telzo2000/cool642tb/img/img00017.jpg

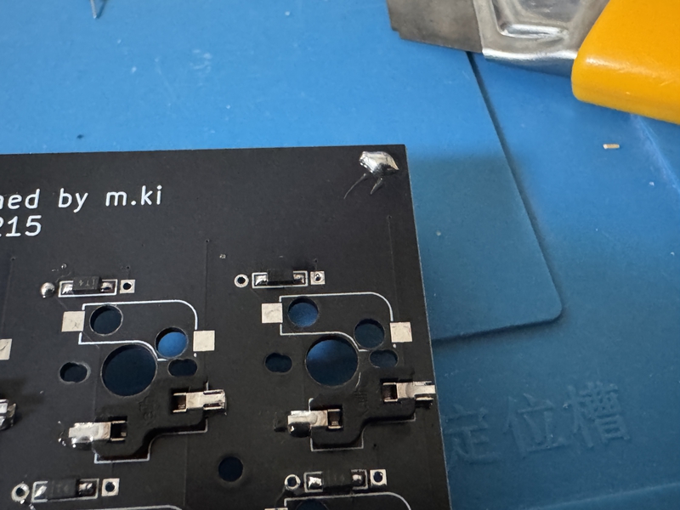
img/img00017.jpg
