telzo2000/cool642tb/img/img00023.jpg

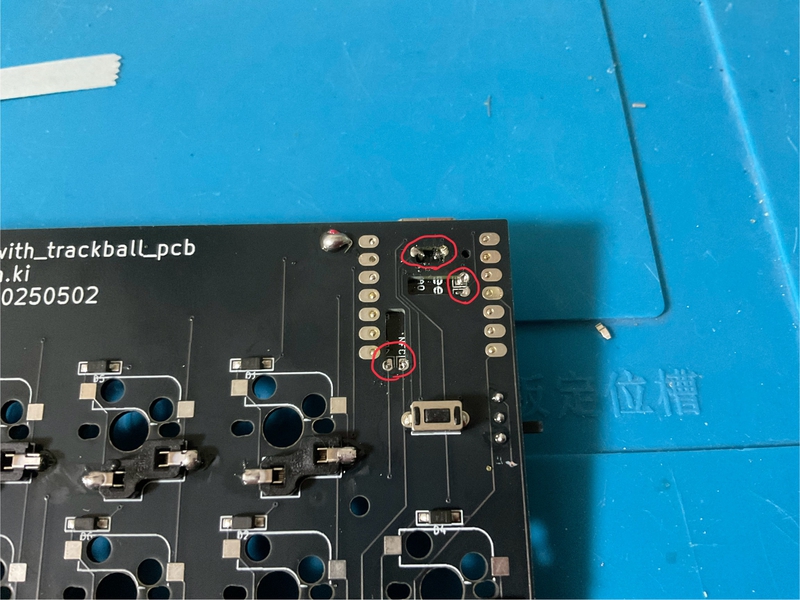
img/img00023.jpg
