telzo2000/cool642tb/img/img00024.jpg

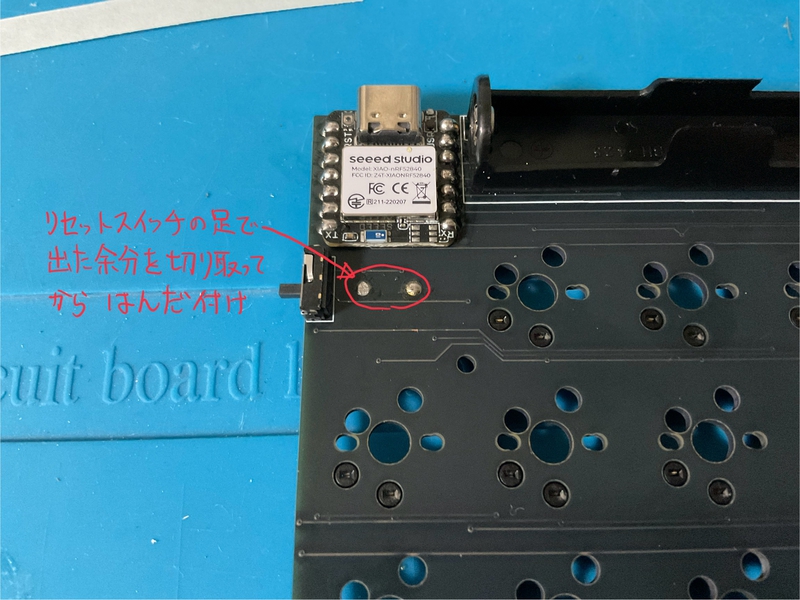
img/img00024.jpg
