telzo2000/cool642tb/case_design/V120/xiao_cover_for_cool642tb v2.3mf

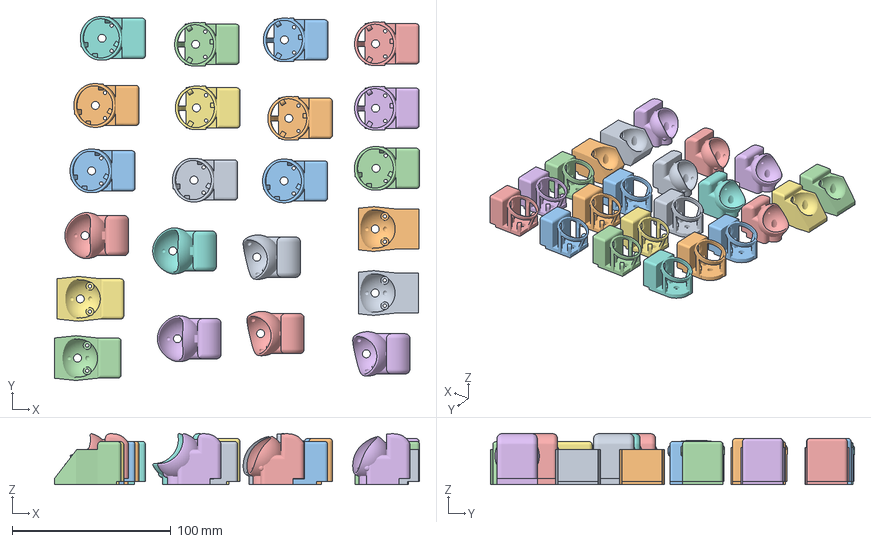
[picture p23: CAD file, 2025-04-20, an earlier design]
case_design/V120/xiao_cover_for_cool642tb v2.3mf
230.1 x 229.4 x 32.2 mm
cool642tb_trackball_case_25mm_type_B.stl x 2
cool642tb_trackball_case_25mm_with_ball_bearing_2.stl x 6
cool642tb_trackball_case_25mm_with_ball_bearing_1.stl x 6
cool642tb_trackball_case_25mm_type_A.stl x 2
cool942tb_trackball_case_type_a.stl x 3
cool942tb_trackball_case_type_b.stl x 3
